mrg-mex/Proyecto_02_semestre_2023-1/CAD/untitled.359.jpg

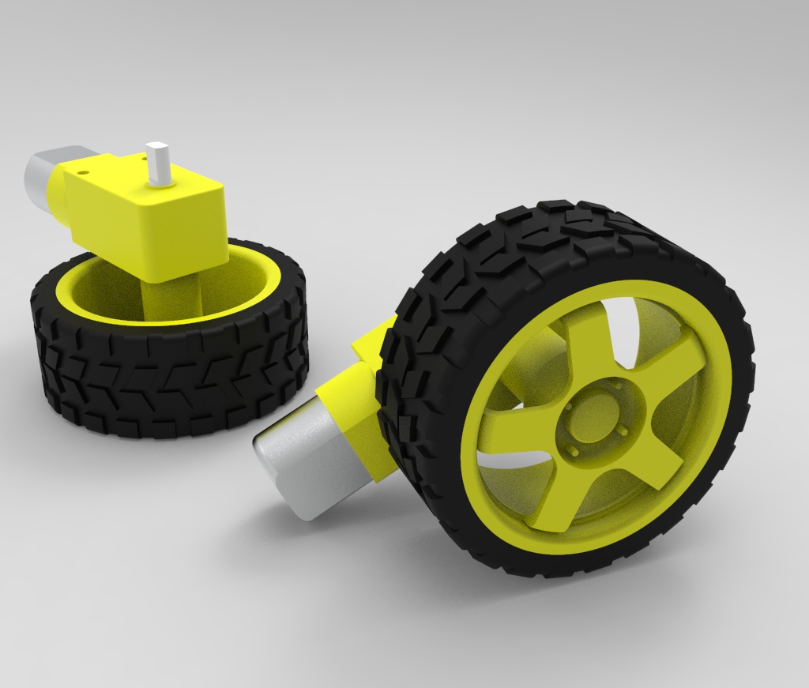
CAD/untitled.359.jpg
