mrg-mex/Proyecto_02_semestre_2023-1/CAD/dc_motor_with_wheel_2.jpg

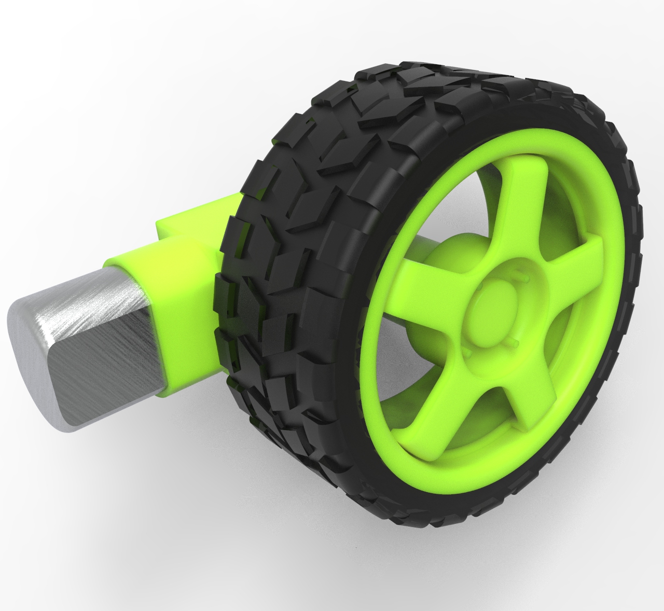
CAD/dc_motor_with_wheel_2.jpg
