mrg-mex/Proyecto_02_semestre_2023-1/CAD/IMG_20200306_232036.jpg

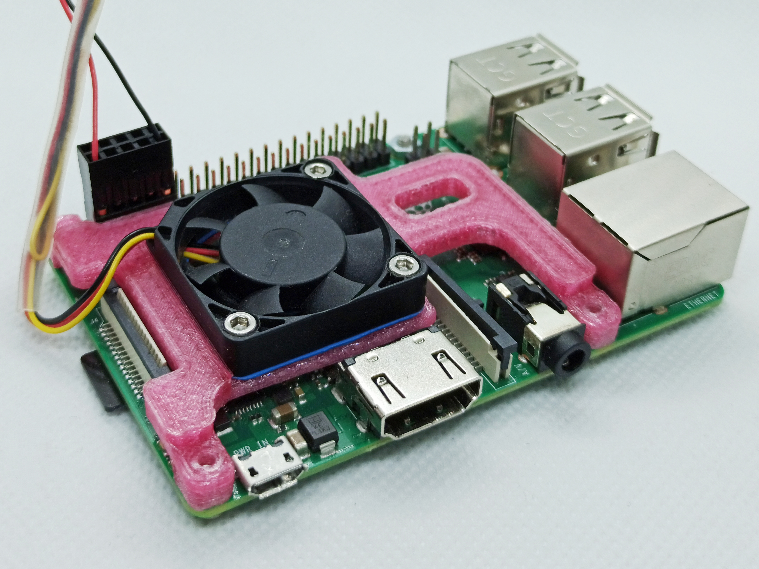
CAD/IMG_20200306_232036.jpg
