mrg-mex/Proyecto_02_semestre_2023-1/CAD/Caster_shroun_65.SLDPRT

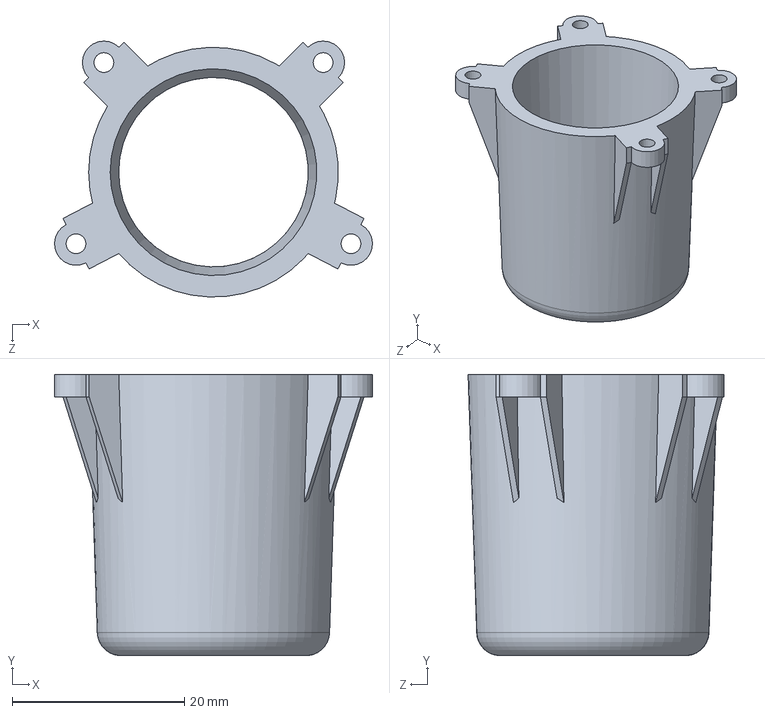
[picture p21: CAD file, 2022-12-22]
CAD/Caster_shroun_65.SLDPRT
36.9 x 32.7 x 29.7 mm
