mrg-mex/Proyecto_02_semestre_2023-1/CAD/Raspberry/2. card slot/card slot part 2 metal pin.SLDPRT

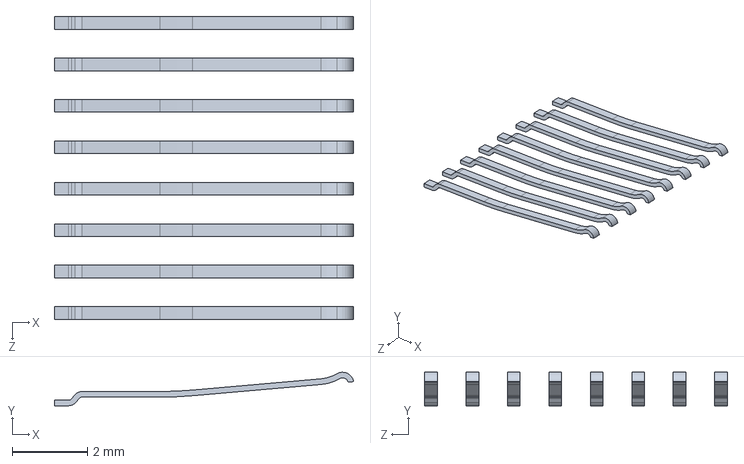
[picture p22: CAD file, 2022-12-05]
CAD/Raspberry/2. card slot/card slot part 2 metal pin.SLDPRT
7.95 x 0.892 x 8.04 mm
