mrg-mex/Proyecto_02_semestre_2023-1/CAD/Raspberry/3.0 PIN HEADER 20.SLDPRT

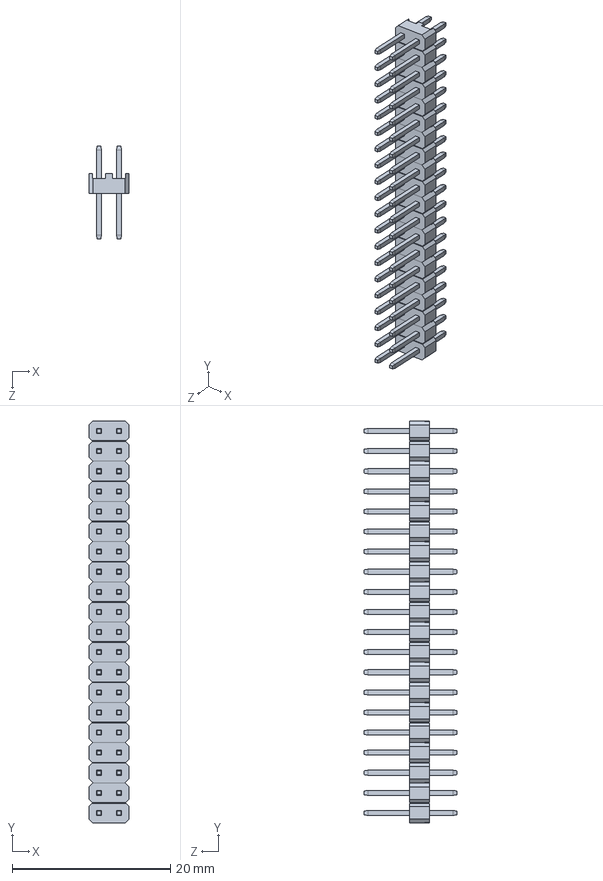
[picture p23: CAD file, 2022-12-05]
CAD/Raspberry/3.0 PIN HEADER 20.SLDPRT
5.08 x 50.8 x 11.8 mm
