mrg-mex/Proyecto_02_semestre_2023-1/CAD/Raspberry/Microphone plug/part 4 microphone plug.SLDPRT

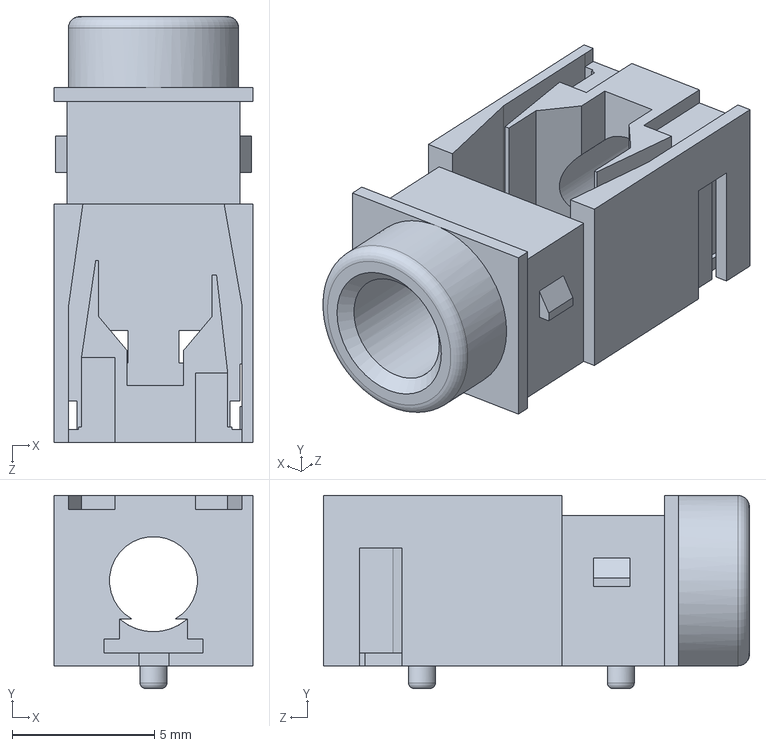
[picture p24: CAD file, 2022-12-05]
CAD/Raspberry/Microphone plug/part 4 microphone plug.SLDPRT
7.00 x 6.80 x 15.0 mm
