mrg-mex/Proyecto_02_semestre_2023-1/CAD/sg90-micro-servomotor-1.snapshot.2/Part1.SLDPRT

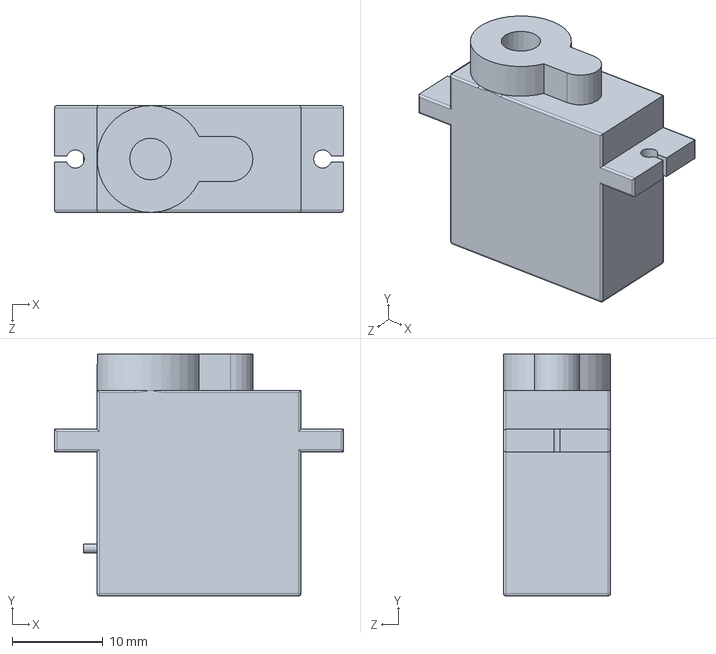
[picture p25: CAD file, 2022-12-05]
CAD/sg90-micro-servomotor-1.snapshot.2/Part1.SLDPRT
31.9 x 26.7 x 11.8 mm
