mrg-mex/Proyecto_02_semestre_2023-1/CAD/Raspberry/1. display connector assembly/2.2 part 2 with combine.SLDPRT

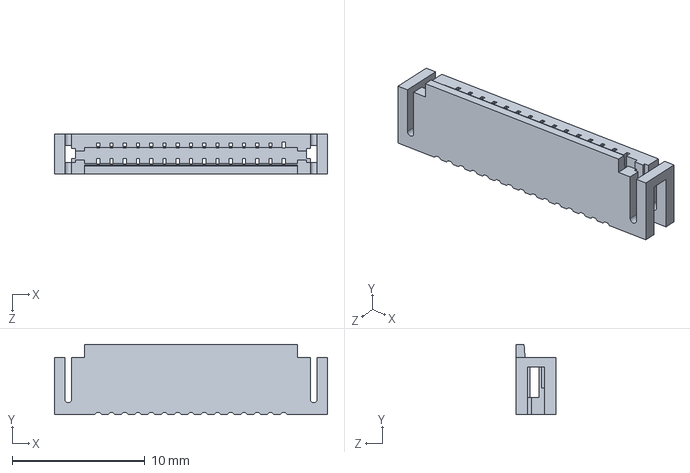
[picture p26: CAD file, 2022-12-05]
CAD/Raspberry/1. display connector assembly/2.2 part 2 with combine.SLDPRT
20.6 x 5.30 x 3.00 mm
