mrg-mex/Proyecto_02_semestre_2023-1/CAD/Raspberry/7.0 MxL.SLDPRT

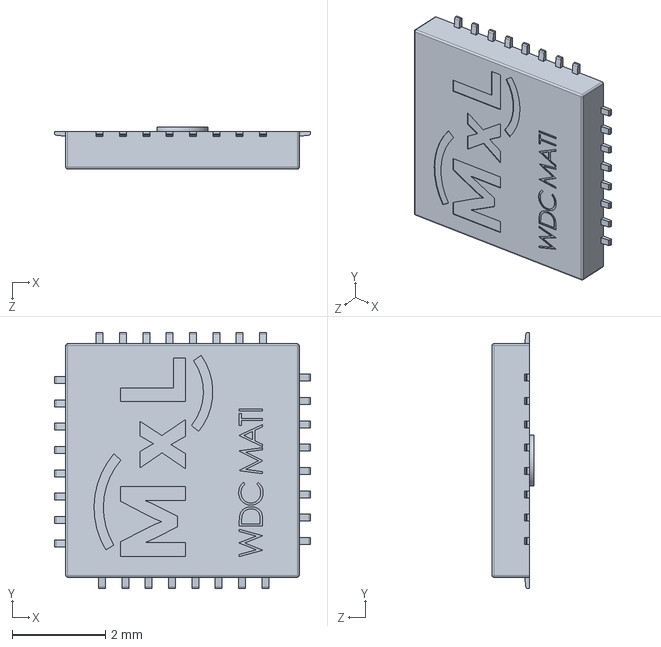
[picture p27: CAD file, 2022-12-05]
CAD/Raspberry/7.0 MxL.SLDPRT
5.48 x 5.48 x 0.9 mm
