mrg-mex/Proyecto_02_semestre_2023-1/CAD/Raspberry/Microphone plug/Microphone plug part 1.SLDPRT

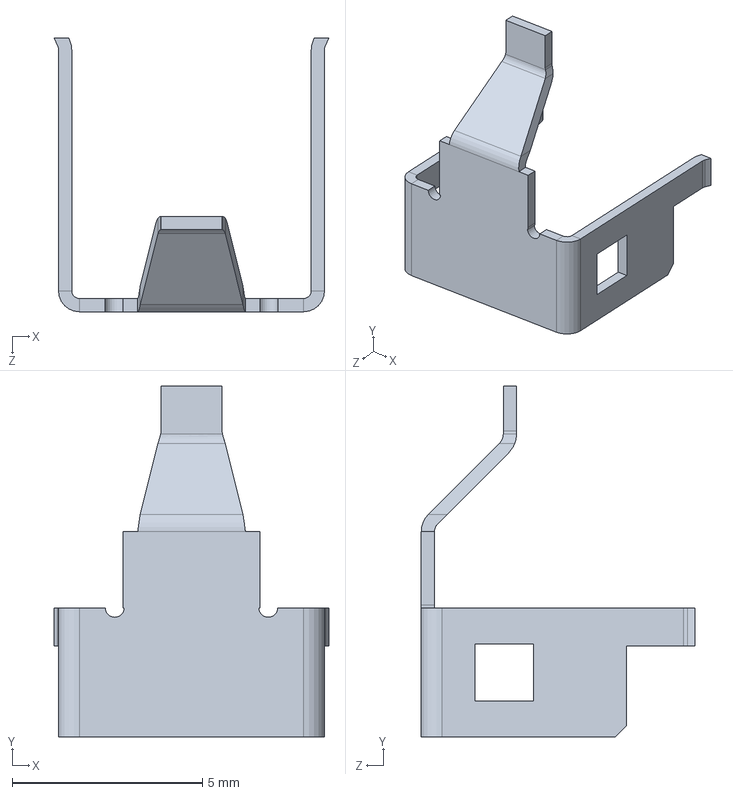
[picture p28: CAD file, 2022-12-05]
CAD/Raspberry/Microphone plug/Microphone plug part 1.SLDPRT
7.23 x 9.23 x 7.20 mm
