mrg-mex/Proyecto_02_semestre_2023-1/CAD/UltrasonicoSoloFrontal.SLDPRT

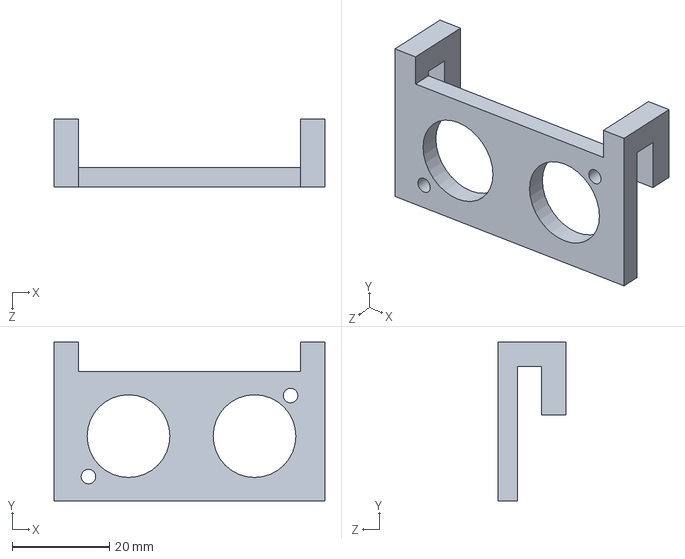
[picture p29: CAD file, 2022-12-22]
CAD/UltrasonicoSoloFrontal.SLDPRT
55.7 x 32.7 x 14.0 mm
