mrg-mex/Proyecto_02_semestre_2023-1/CAD/Raspberry/1. display connector assembly/1.1 part 1 metal pin.SLDPRT

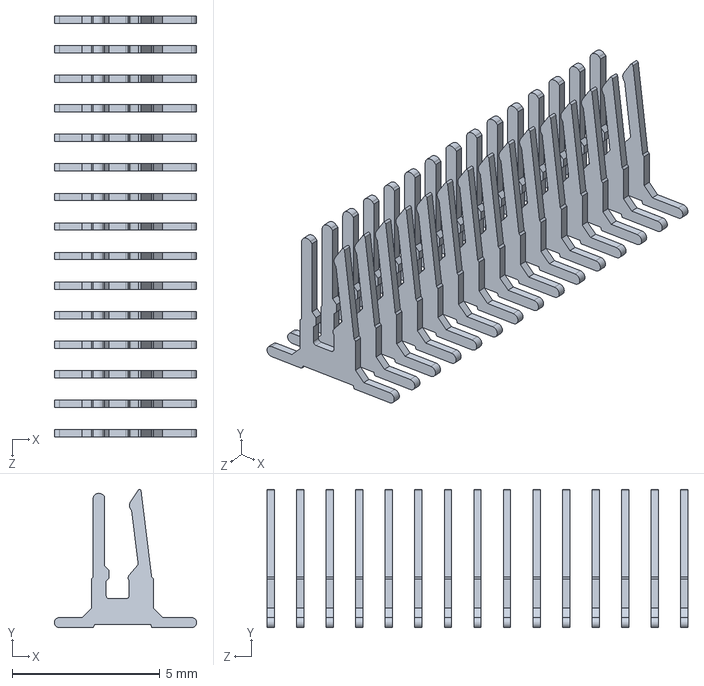
[picture p30: CAD file, 2022-12-05]
CAD/Raspberry/1. display connector assembly/1.1 part 1 metal pin.SLDPRT
4.82 x 4.69 x 14.2 mm
