mrg-mex/Proyecto_02_semestre_2023-1/CAD/Raspberry/2. card slot/sd card slot v1.SLDPRT

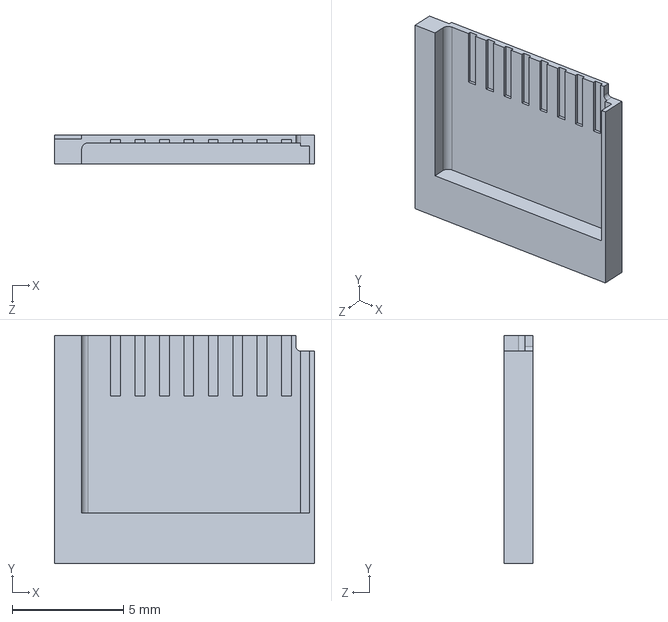
[picture p31: CAD file, 2022-12-05]
CAD/Raspberry/2. card slot/sd card slot v1.SLDPRT
11.7 x 10.3 x 1.30 mm
