mrg-mex/Proyecto_02_semestre_2023-1/CAD/Raspberry/2.0. PIN HEADER  one.SLDPRT

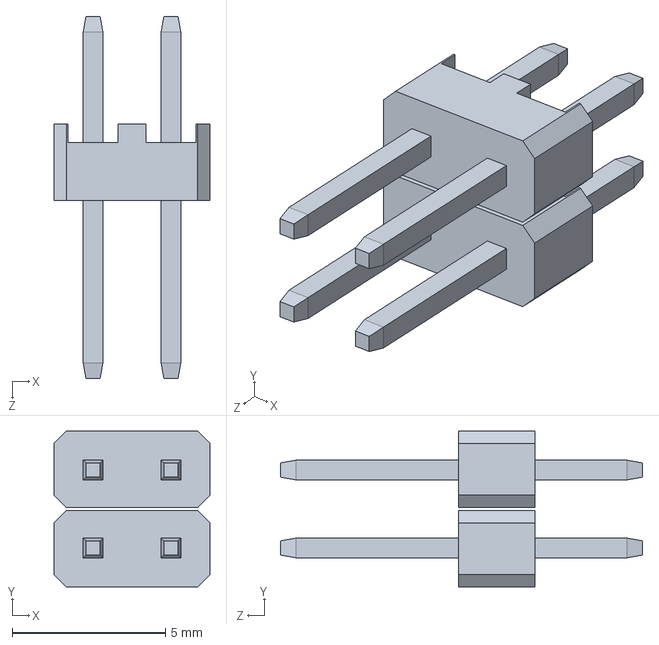
[picture p32: CAD file, 2022-12-05]
CAD/Raspberry/2.0. PIN HEADER one.SLDPRT
5.08 x 5.08 x 11.8 mm
