mrg-mex/Proyecto_02_semestre_2023-1/CAD/Raspberry/Microphone plug/part 2 microphon plug metal.SLDPRT

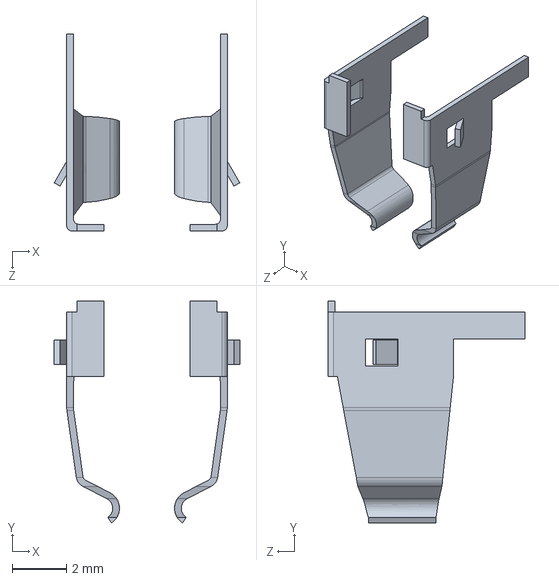
[picture p33: CAD file, 2022-12-05]
CAD/Raspberry/Microphone plug/part 2 microphon plug metal.SLDPRT
6.87 x 8.22 x 7.30 mm
