mrg-mex/Proyecto_02_semestre_2023-1/CAD/UltrasonicoSolo.SLDPRT

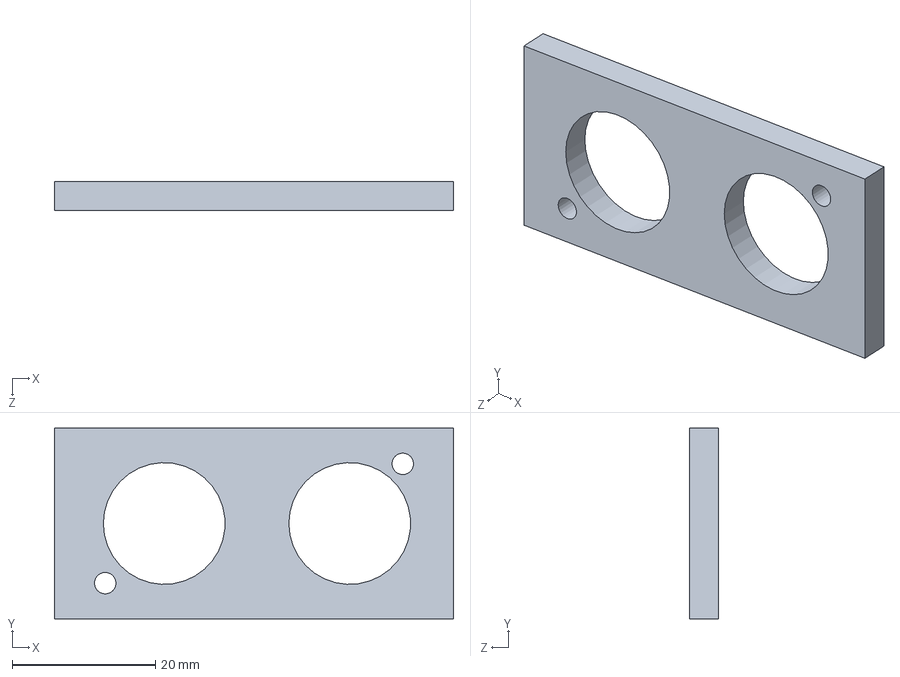
[picture p34: CAD file, 2022-12-22]
CAD/UltrasonicoSolo.SLDPRT
55.7 x 26.7 x 4.00 mm
