mrg-mex/Proyecto_02_semestre_2023-1/CAD/hc sr04 ultrasonic sensor.SLDPRT

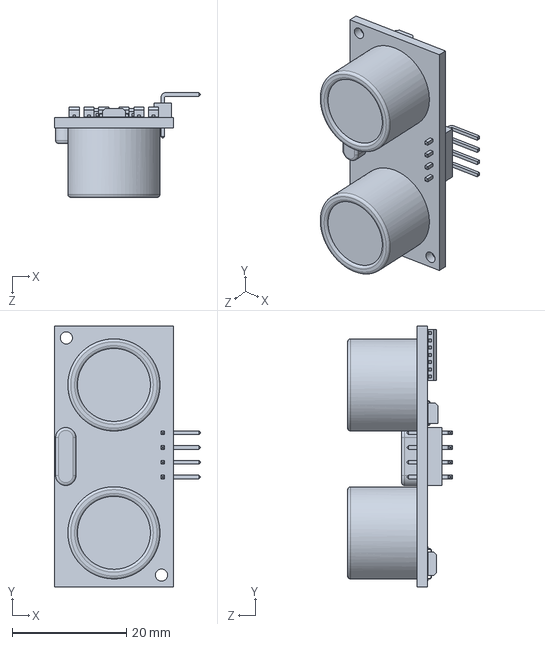
[picture p35: CAD file, 2022-12-22]
CAD/hc sr04 ultrasonic sensor.SLDPRT
25.6 x 45.7 x 18.4 mm
