mrg-mex/Proyecto_02_semestre_2023-1/CAD/Raspberry/9.0 VLI PCIe USB 3.0 Controller.SLDPRT

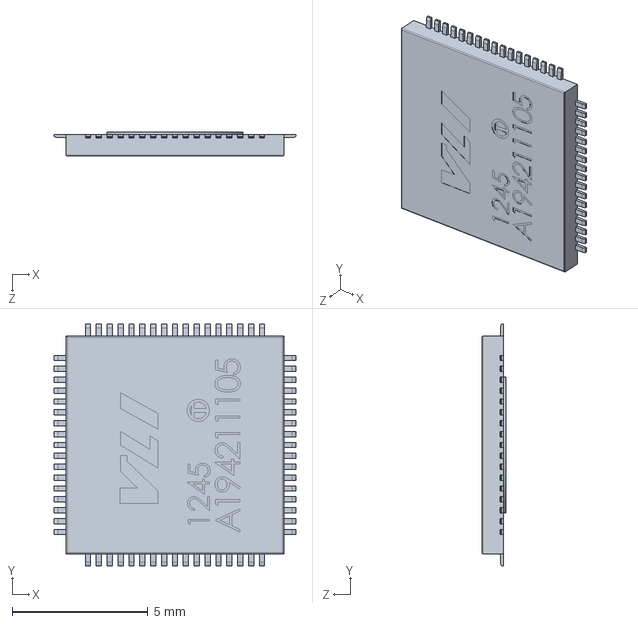
[picture p36: CAD file, 2022-12-05]
CAD/Raspberry/9.0 VLI PCIe USB 3.0 Controller.SLDPRT
8.90 x 8.90 x 0.9 mm
