mrg-mex/Proyecto_02_semestre_2023-1/CAD/sg90-micro-servomotor-1.snapshot.2/sg90 micro servo.STEP

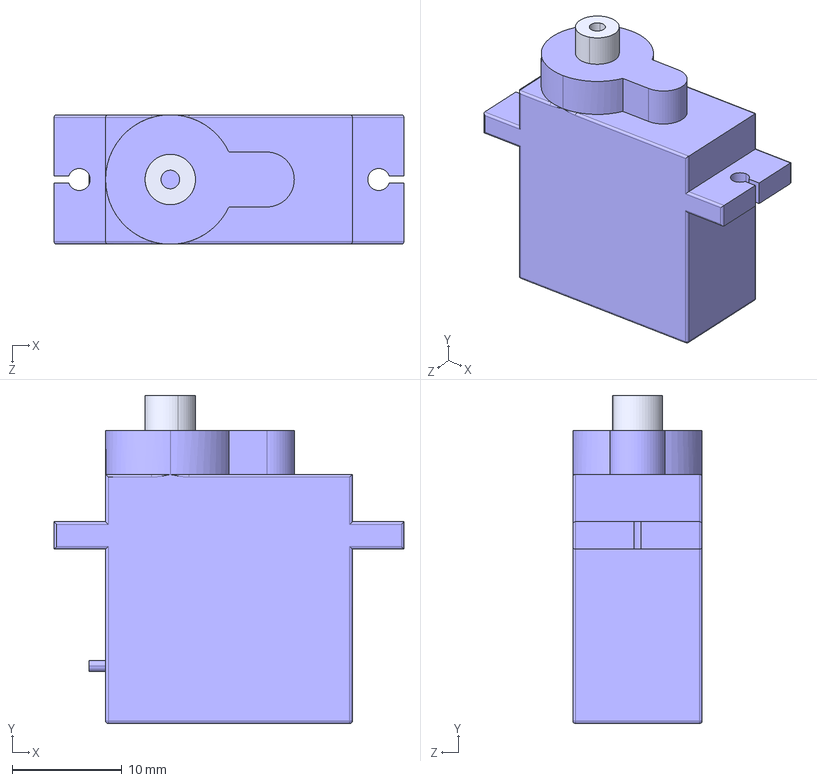
[picture p37: CAD file, 2022-12-05]
CAD/sg90-micro-servomotor-1.snapshot.2/sg90 micro servo.STEP
31.9 x 29.9 x 11.8 mm
axis.step
