mrg-mex/Proyecto_02_semestre_2023-1/CAD/Agarradera.SLDPRT

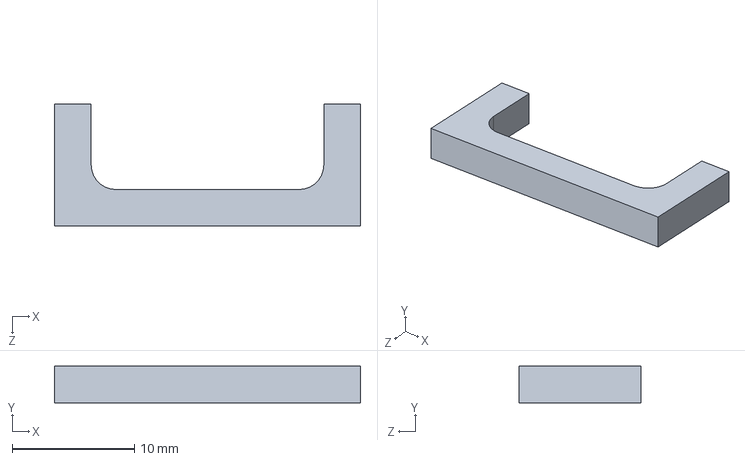
[picture p38: CAD file, 2022-12-21]
CAD/Agarradera.SLDPRT
25.0 x 3.00 x 10.0 mm
