mrg-mex/Proyecto_02_semestre_2023-1/CAD/Raspberry/15.0   2x USB 2.0 PORT.SLDPRT

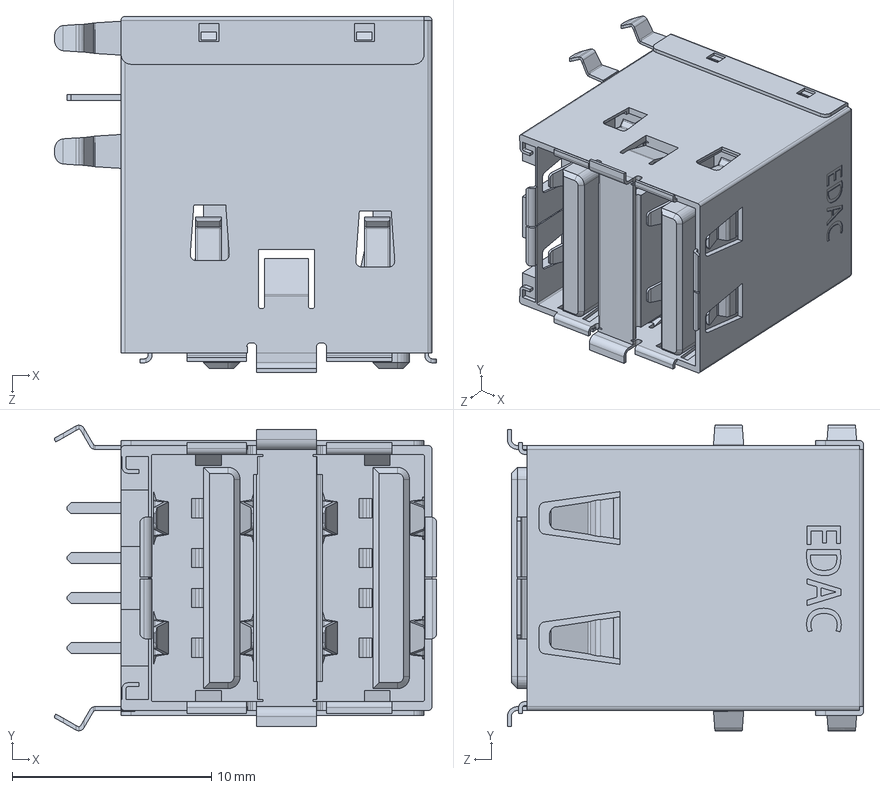
[picture p39: CAD file, 2022-12-05]
CAD/Raspberry/15.0 2x USB 2.0 PORT.SLDPRT
19.2 x 15.3 x 17.9 mm
