mrg-mex/Proyecto_02_semestre_2023-1/CAD/Raspberry/10.0 Female USB connector.SLDPRT

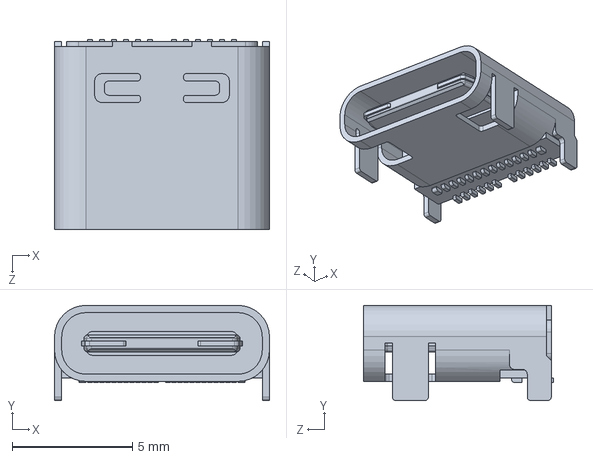
[picture p40: CAD file, 2022-12-05]
CAD/Raspberry/10.0 Female USB connector.SLDPRT
8.94 x 3.96 x 7.90 mm
