mrg-mex/Proyecto_02_semestre_2023-1/CAD/SoportePuenteH.SLDPRT

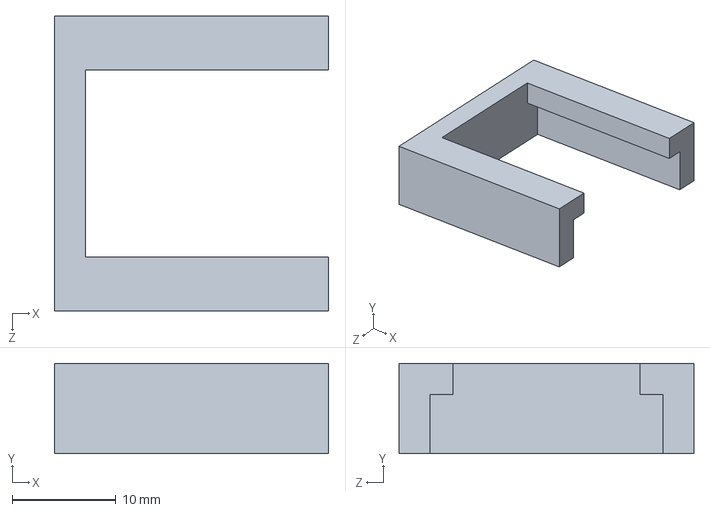
[picture p41: CAD file, 2022-12-21]
CAD/SoportePuenteH.SLDPRT
26.4 x 8.70 x 28.4 mm
