mrg-mex/Proyecto_02_semestre_2023-1/CAD/dc_motor_and_wheel.STEP

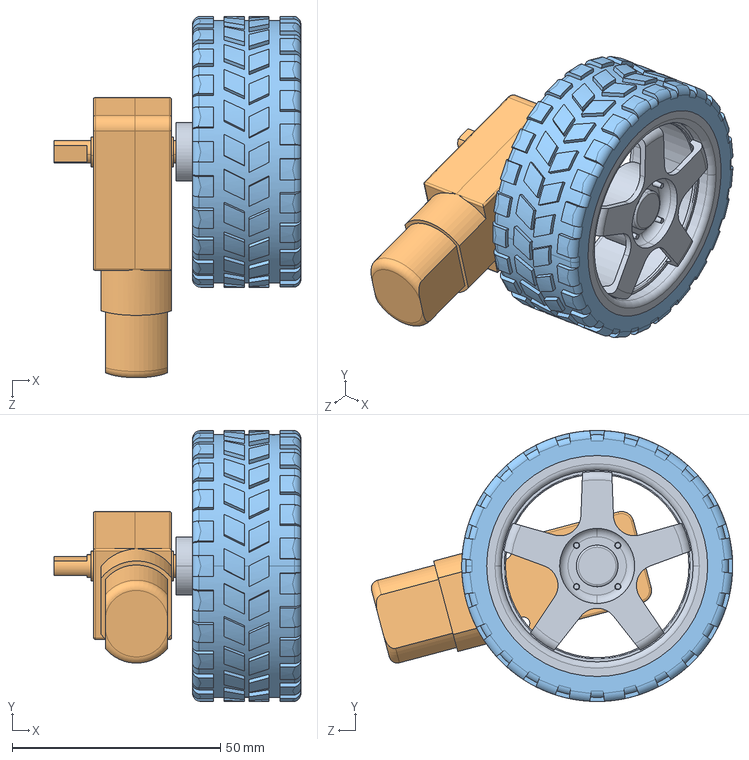
[picture p42: CAD file, 2022-12-05]
CAD/dc_motor_and_wheel.STEP
59.2 x 65.0 x 86.7 mm
