mrg-mex/Proyecto_02_semestre_2023-1/CAD/Raspberry/5.0 CPU Broadcom.SLDPRT

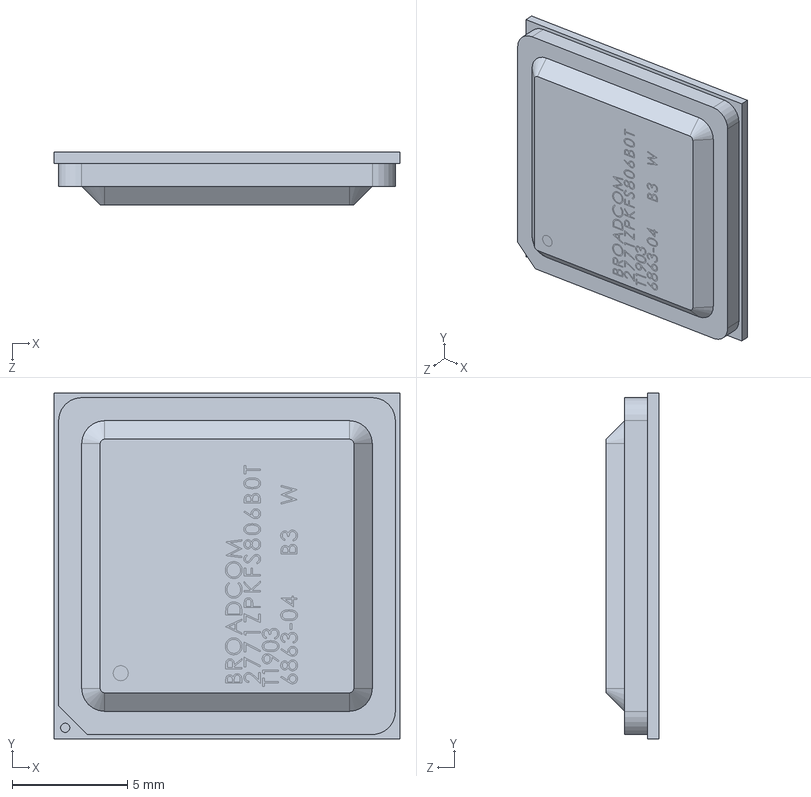
[picture p43: CAD file, 2022-12-05]
CAD/Raspberry/5.0 CPU Broadcom.SLDPRT
15.0 x 15.0 x 2.30 mm
