mrg-mex/Proyecto_02_semestre_2023-1/CAD/Raspberry/14.0  2x USB 3.0 PORT.SLDPRT

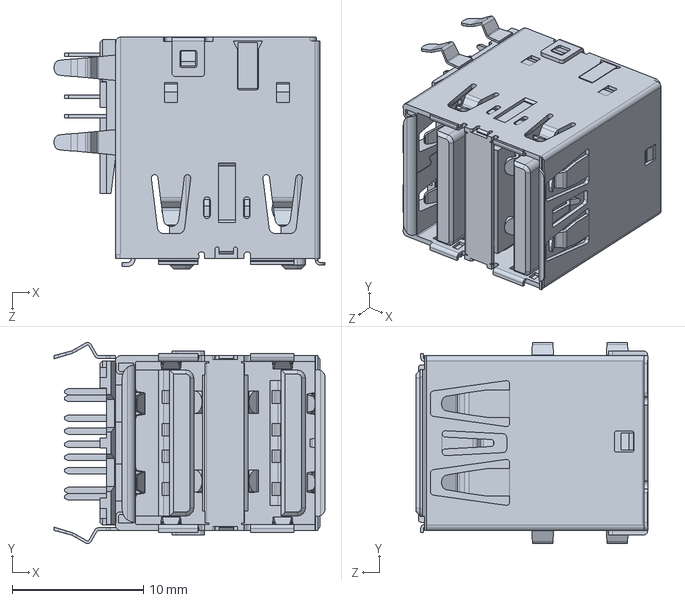
[picture p44: CAD file, 2022-12-05]
CAD/Raspberry/14.0 2x USB 3.0 PORT.SLDPRT
20.6 x 15.3 x 17.7 mm
