mrg-mex/Proyecto_02_semestre_2023-1/CAD/Raspberry/4.0 metal plate..SLDPRT

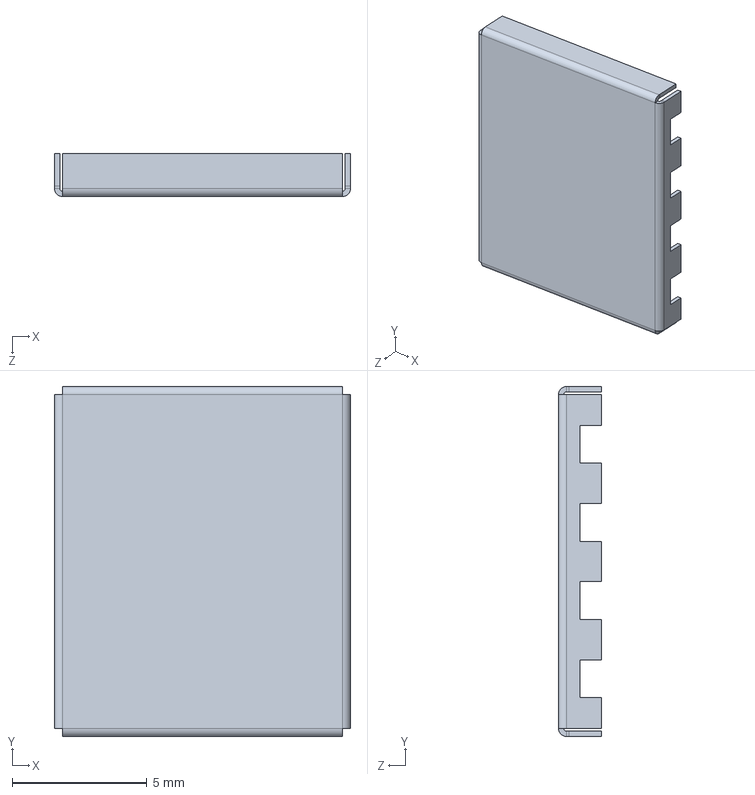
[picture p45: CAD file, 2022-12-05]
CAD/Raspberry/4.0 metal plate..SLDPRT
11.0 x 13.0 x 1.60 mm
