mrg-mex/Proyecto_02_semestre_2023-1/CAD/Base_cam.SLDPRT

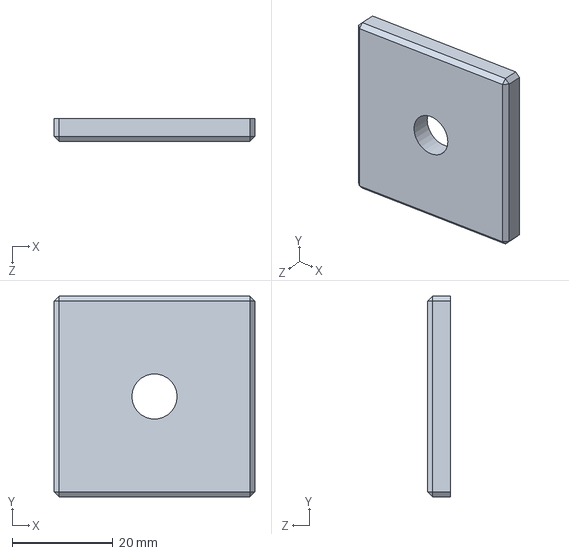
[picture p46: CAD file, 2022-12-05]
CAD/Base_cam.SLDPRT
40.0 x 40.0 x 4.50 mm
