mrg-mex/Proyecto_02_semestre_2023-1/CAD/caster_base_65mm.SLDPRT

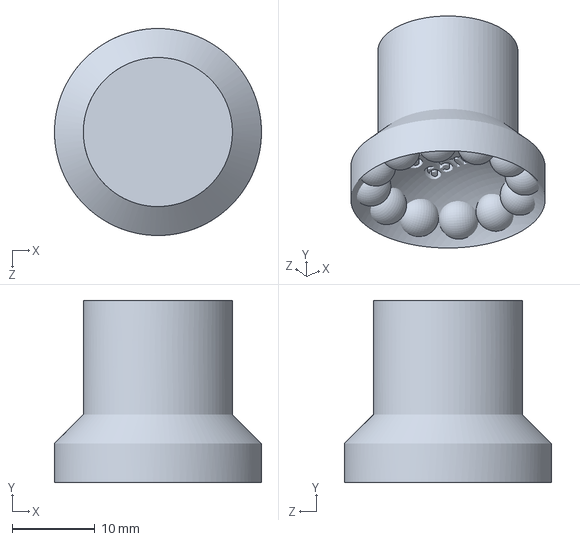
[picture p47: CAD file, 2022-12-05]
CAD/caster_base_65mm.SLDPRT
25.0 x 22.0 x 25.0 mm
