mrg-mex/Proyecto_02_semestre_2023-1/CAD/Raspberry/9.0 VLI PCIe USB 3.0 Controller v1.SLDPRT

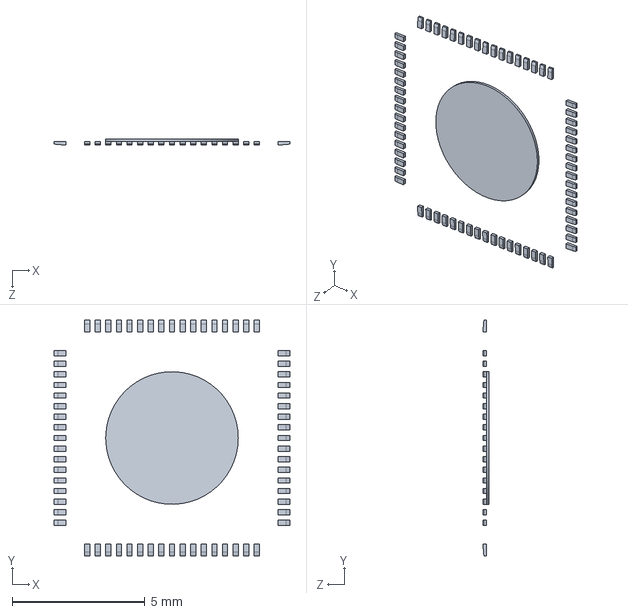
[picture p48: CAD file, 2022-12-05]
CAD/Raspberry/9.0 VLI PCIe USB 3.0 Controller v1.SLDPRT
8.90 x 8.90 x 0.222 mm
