mrg-mex/Proyecto_02_semestre_2023-1/CAD/Raspberry/8.0 Gigabit Ethernet Transceiver.SLDPRT

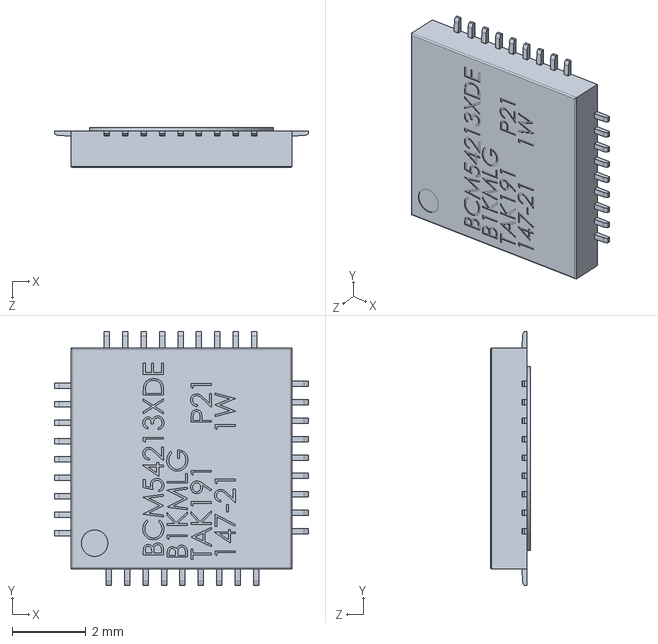
[picture p49: CAD file, 2022-12-05]
CAD/Raspberry/8.0 Gigabit Ethernet Transceiver.SLDPRT
6.90 x 6.90 x 1.10 mm
