mrg-mex/Proyecto_02_semestre_2023-1/CAD/AprilTag.SLDPRT

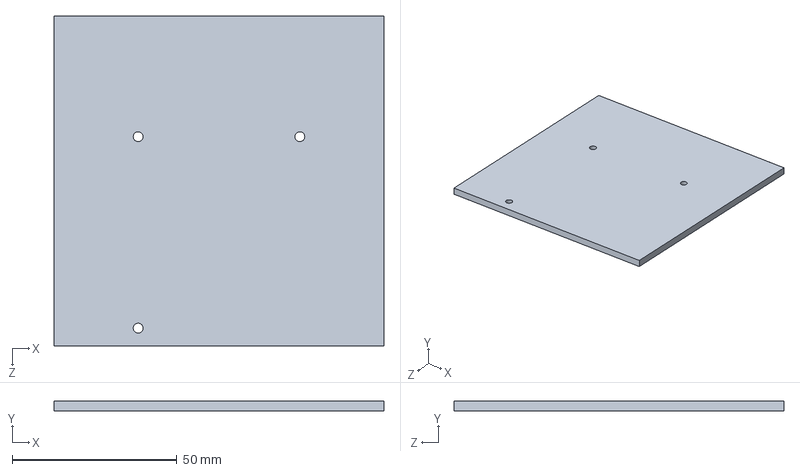
[picture p50: CAD file, 2022-12-05]
CAD/AprilTag.SLDPRT
100.0 x 3.00 x 100.0 mm
