mrg-mex/Proyecto_02_semestre_2023-1/CAD/Raspberry/1.0 Plate raspberry Pi 4.SLDPRT

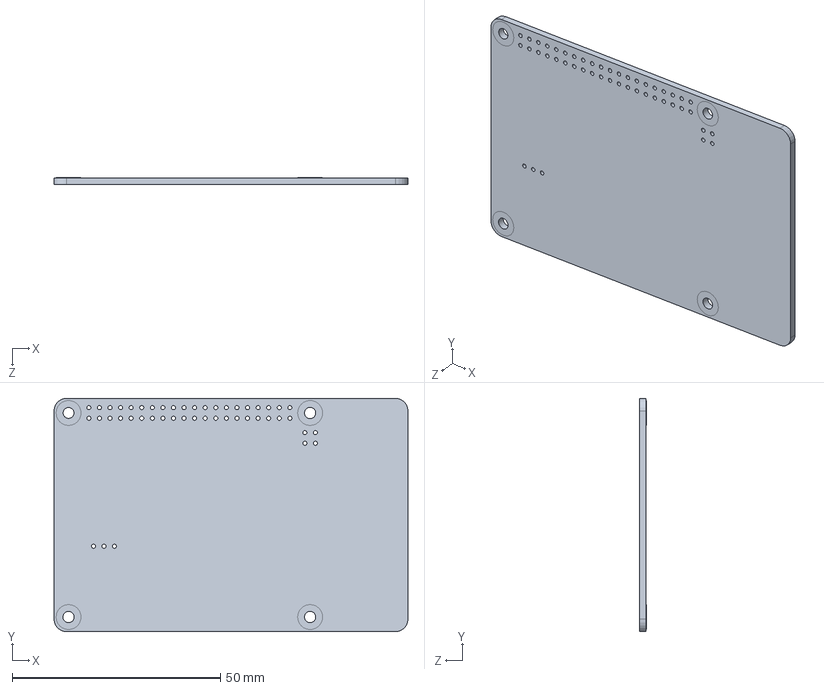
[picture p51: CAD file, 2022-12-05]
CAD/Raspberry/1.0 Plate raspberry Pi 4.SLDPRT
85.0 x 56.0 x 1.70 mm
