mrg-mex/Proyecto_02_semestre_2023-1/CAD/Body_cam.SLDPRT

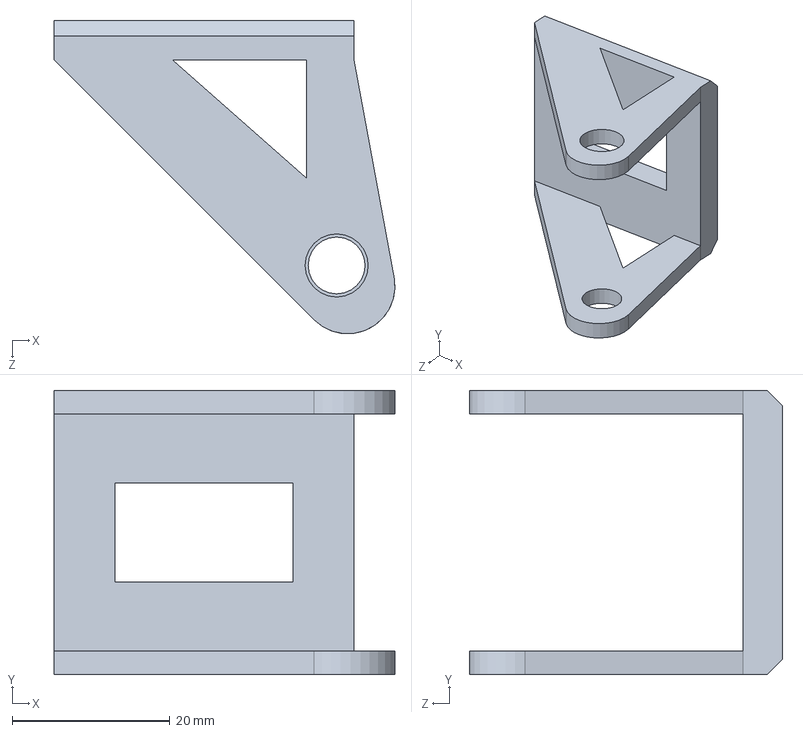
[picture p52: CAD file, 2022-12-05]
CAD/Body_cam.SLDPRT
43.2 x 36.0 x 39.7 mm
