mrg-mex/Proyecto_02_semestre_2023-1/CAD/SG90 Servo.STEP

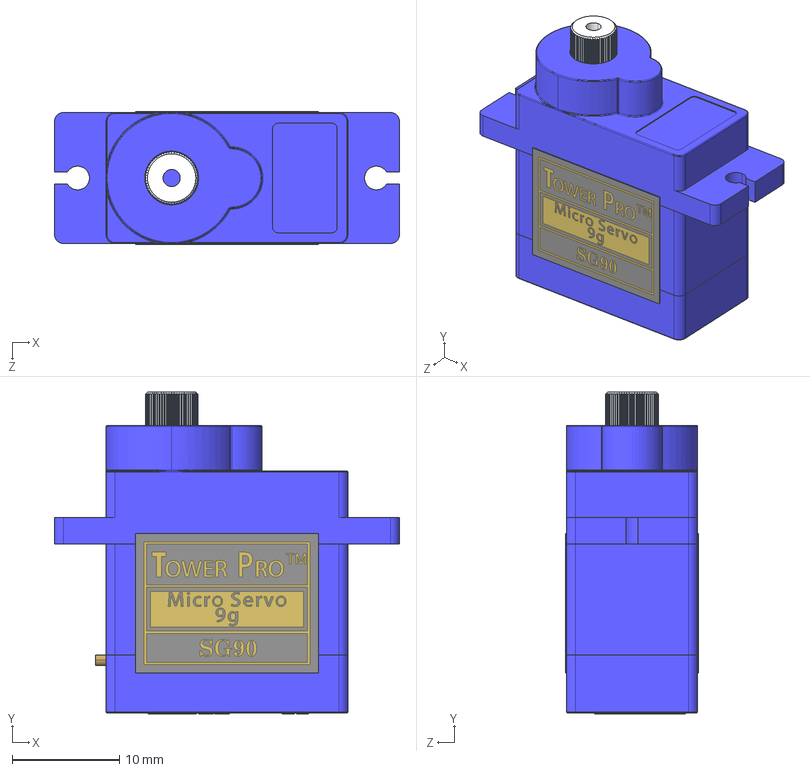
[picture p53: CAD file, 2022-12-05]
CAD/SG90 Servo.STEP
32.1 x 29.9 x 12.4 mm
