mrg-mex/Proyecto_02_semestre_2023-1/CAD/batery.SLDPRT

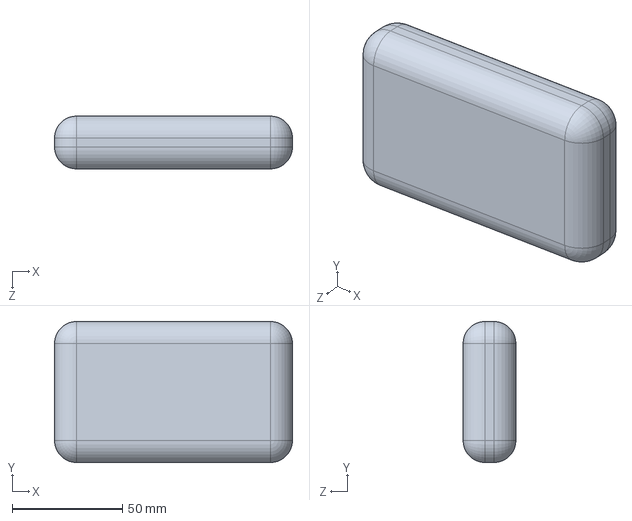
[picture p54: CAD file, 2022-12-05]
CAD/batery.SLDPRT
108.0 x 64.0 x 24.0 mm
