mrg-mex/Proyecto_02_semestre_2023-1/CAD/Soporte_ventilador.SLDPRT

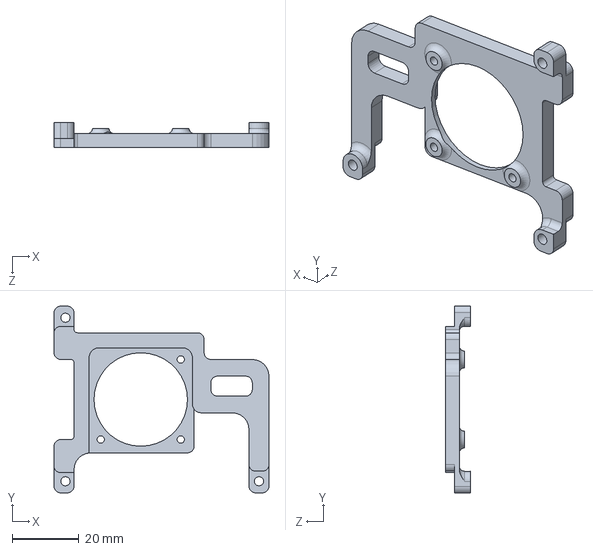
[picture p55: CAD file, 2022-12-05]
CAD/Soporte_ventilador.SLDPRT
64.4 x 56.0 x 7.60 mm
