mrg-mex/Proyecto_02_semestre_2023-1/CAD/Cam_servo.SLDPRT

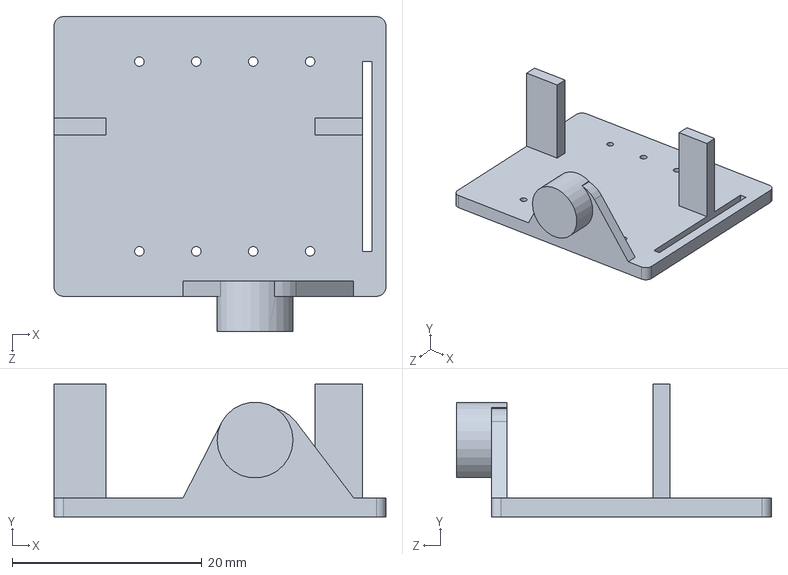
[picture p56: CAD file, 2022-12-05]
CAD/Cam_servo.SLDPRT
35.0 x 14.0 x 33.2 mm
