mrg-mex/Proyecto_02_semestre_2023-1/CAD/Caster_base_65.SLDPRT

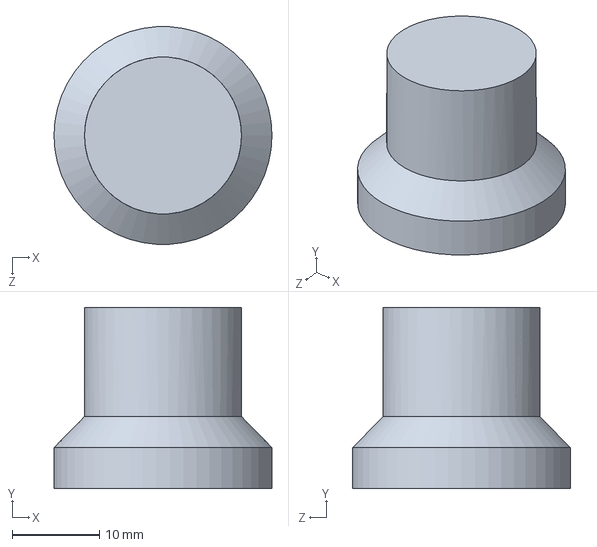
[picture p57: CAD file, 2022-12-05]
CAD/Caster_base_65.SLDPRT
25.0 x 20.8 x 25.0 mm
