mrg-mex/Proyecto_02_semestre_2023-1/CAD/Fan_30x30x8_5V_2pin.stp

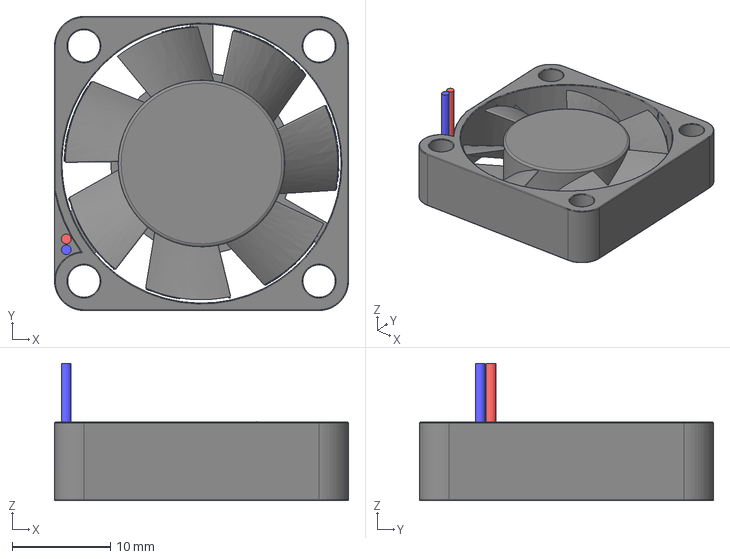
[picture p58: CAD file, 2022-12-05]
CAD/Fan_30x30x8_5V_2pin.stp
30.0 x 30.0 x 14.0 mm
Rotator
