mrg-mex/Proyecto_02_semestre_2023-1/CAD/Ball_2_5.SLDPRT

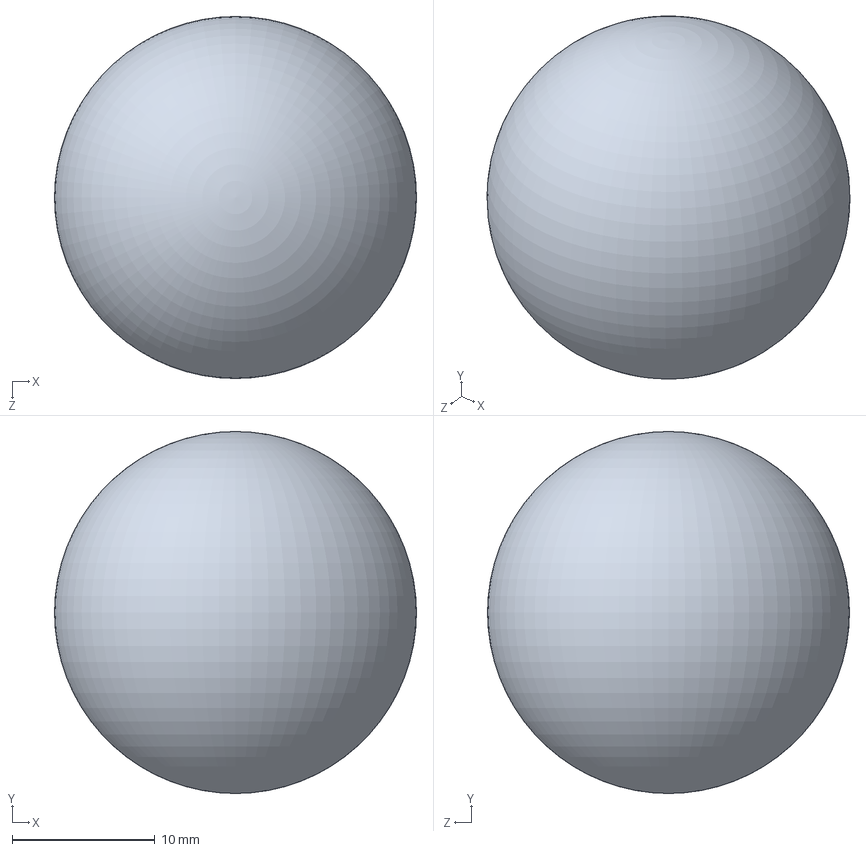
[picture p59: CAD file, 2022-12-05]
CAD/Ball_2_5.SLDPRT
25.4 x 25.4 x 25.4 mm
