mrg-mex/Proyecto_02_semestre_2023-1/CAD/Arducam16MPCamera.SLDPRT

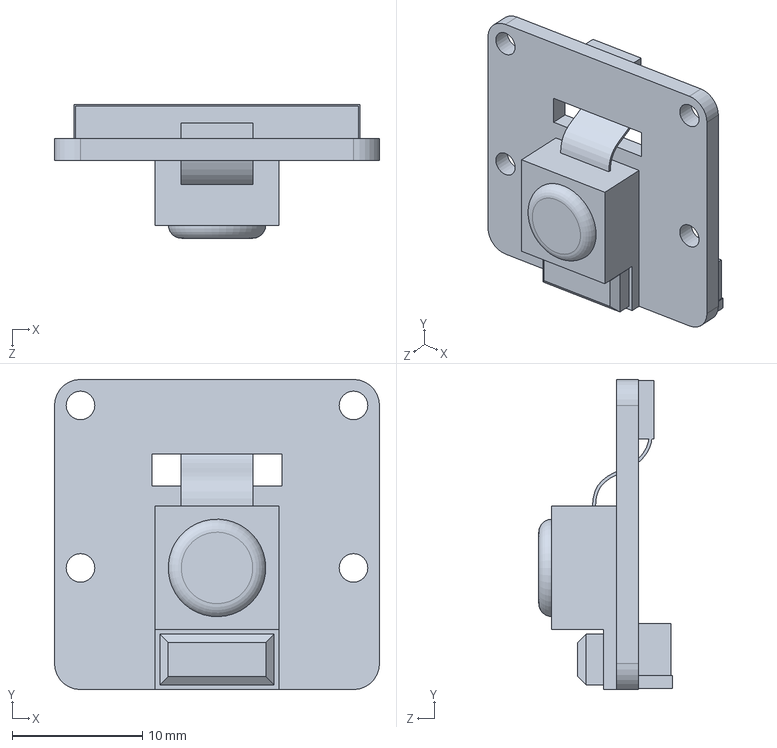
[picture p60: CAD file, 2022-12-05]
CAD/Arducam16MPCamera.SLDPRT
25.0 x 23.9 x 10.3 mm
