mrg-mex/Proyecto_02_semestre_2023-1/CAD/Rasberry_dummy.SLDPRT

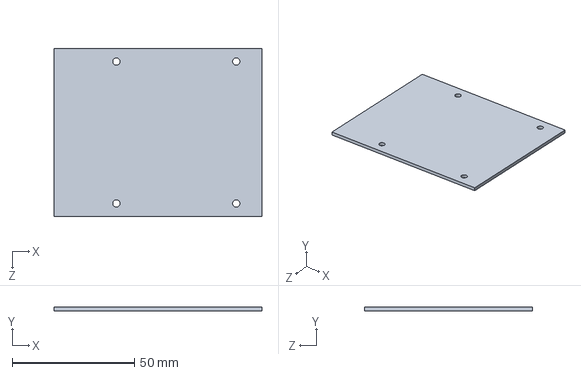
[picture p61: CAD file, 2022-12-05]
CAD/Rasberry_dummy.SLDPRT
85.0 x 1.60 x 68.8 mm
