mrg-mex/Proyecto_02_semestre_2023-1/CAD/rpi_vent_v2_fangasket.stp

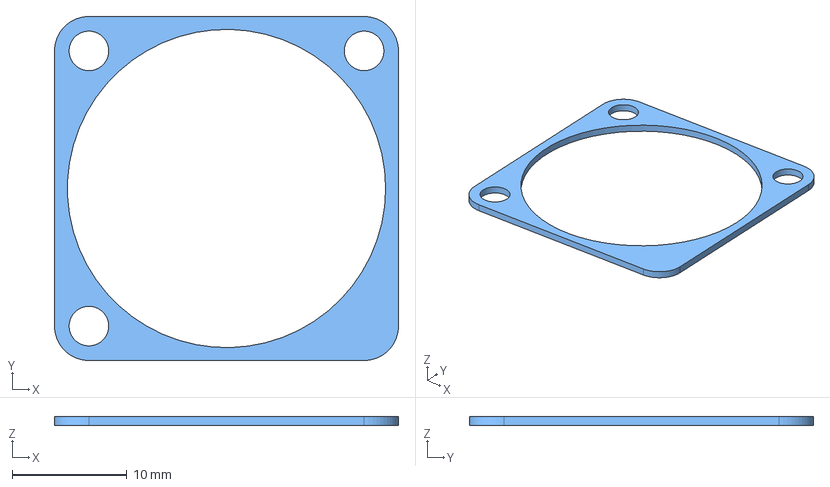
[picture p62: CAD file, 2022-12-05]
CAD/rpi_vent_v2_fangasket.stp
30.0 x 30.0 x 0.8 mm
