mrg-mex/Proyecto_02_semestre_2023-1/CAD/PICO_PinsDown.STEP

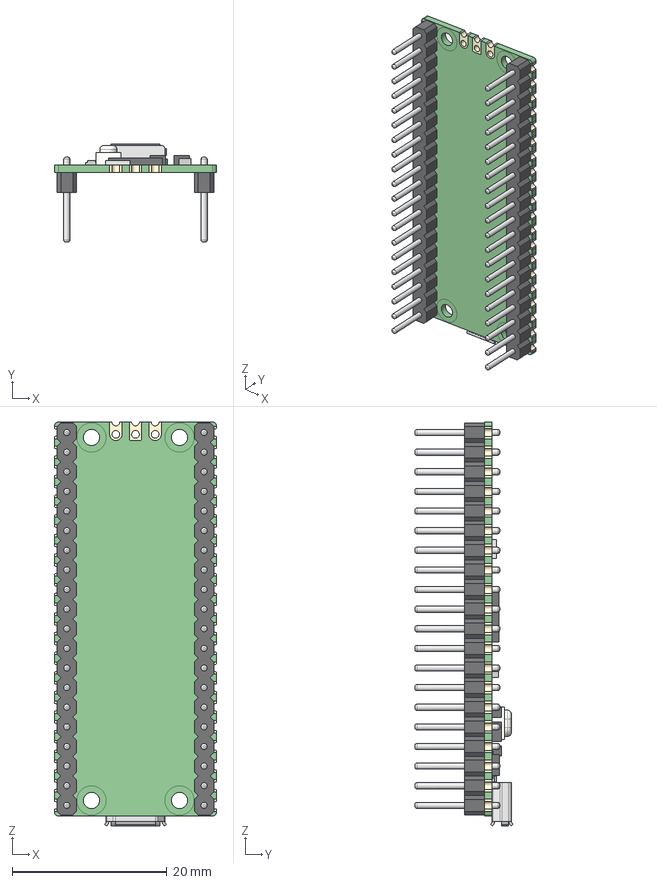
[picture p63: CAD file, 2022-12-05]
CAD/PICO_PinsDown.STEP
21.0 x 12.7 x 52.3 mm
PICO_REF_BOARD.STEP
PICO_REF_USB.STEP
PICO_REF_SWITCH.STEP
PICO_REF_MICROCONTROLLER.STEP
PICO_REF_LED.STEP
PICO_REF_ONSEMI.STEP
PICO_BOURNS.STEP
PICO_MURATA.STEP x 2
PICO_RICHTEK.STEP
PICO_DIODES.STEP
PICO_AEL.STEP
PICO_PIN_HEADERS
PICO_HEADER_HOLES
