mrg-mex/Proyecto_02_semestre_2023-1/CAD/Separador_M2_5.SLDPRT

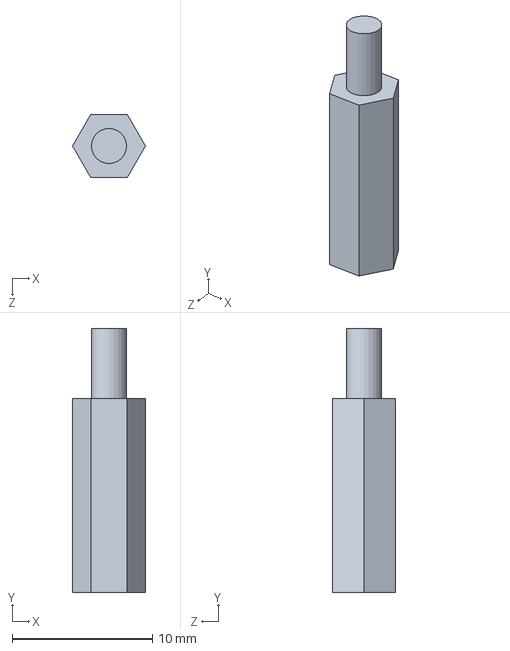
[picture p64: CAD file, 2022-12-05]
CAD/Separador_M2_5.SLDPRT
5.20 x 18.8 x 4.50 mm
