mrg-mex/Proyecto_02_semestre_2023-1/CAD/caster_shroud_65mm.stl

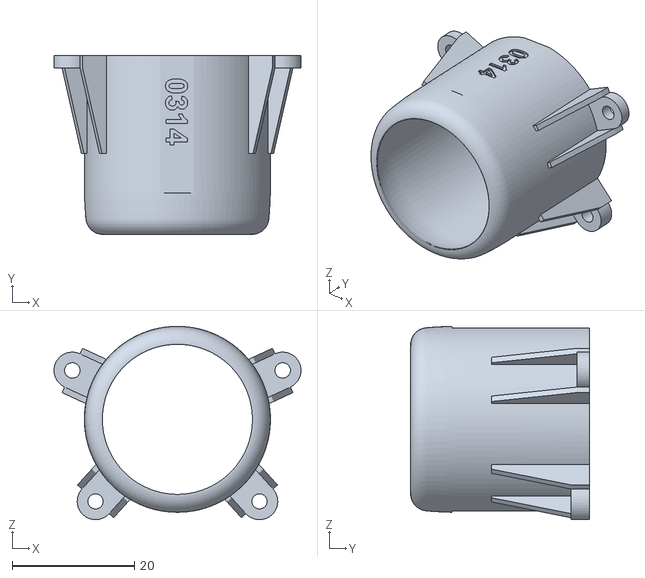
[picture p65: CAD file, 2022-12-05]
CAD/caster_shroud_65mm.stl
40.5 x 29.3 x 31.7
